jedimatt42/tipi/hardware/tipi-speech/kicad/3D/10-Pin Shrouded Header (IDC) Straight.stp

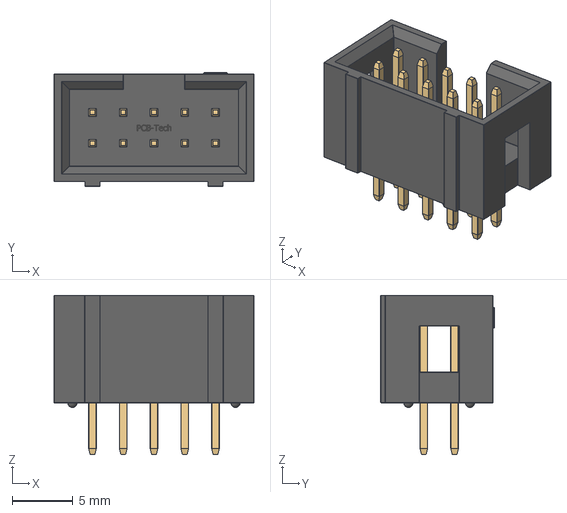
[picture p16: CAD file, 2020-05-09]
hardware/tipi-speech/kicad/3D/10-Pin Shrouded Header (IDC) Straight.stp
16.5 x 9.37 x 13.2 mm
Straight Contact x 10
10-Pin Shrouded Header Body
