jedimatt42/tipi/hardware/tipi-speech/kicad/3D/DS1021-2x5SF11.stp

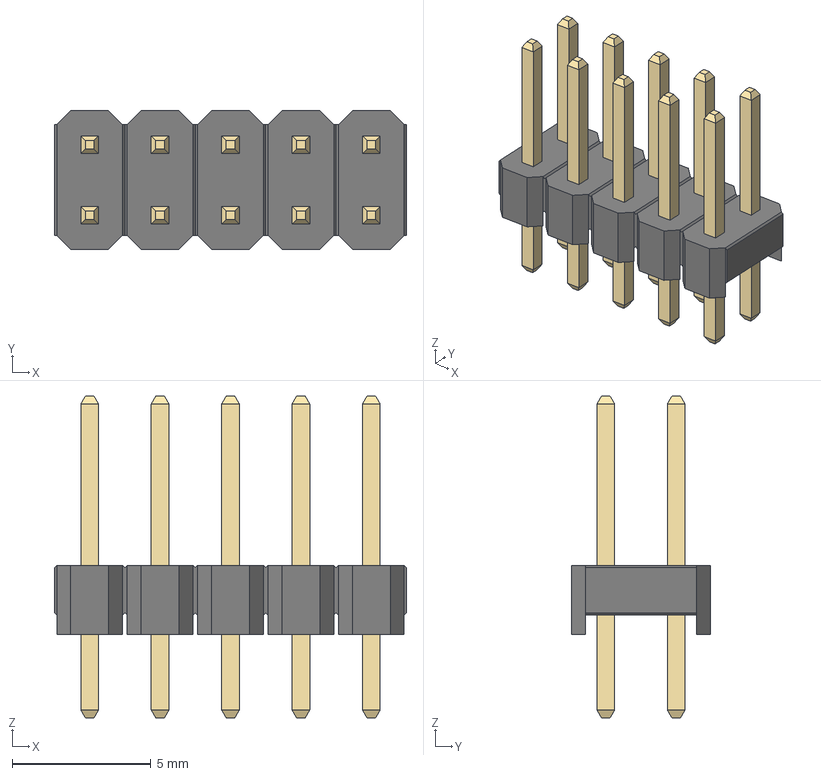
[picture p17: CAD file, 2020-05-09]
hardware/tipi-speech/kicad/3D/DS1021-2x5SF11.stp
12.7 x 5.00 x 11.6 mm
