jedimatt42/tipi/hardware/tipi-speech/kicad/3D/RC0805N.step

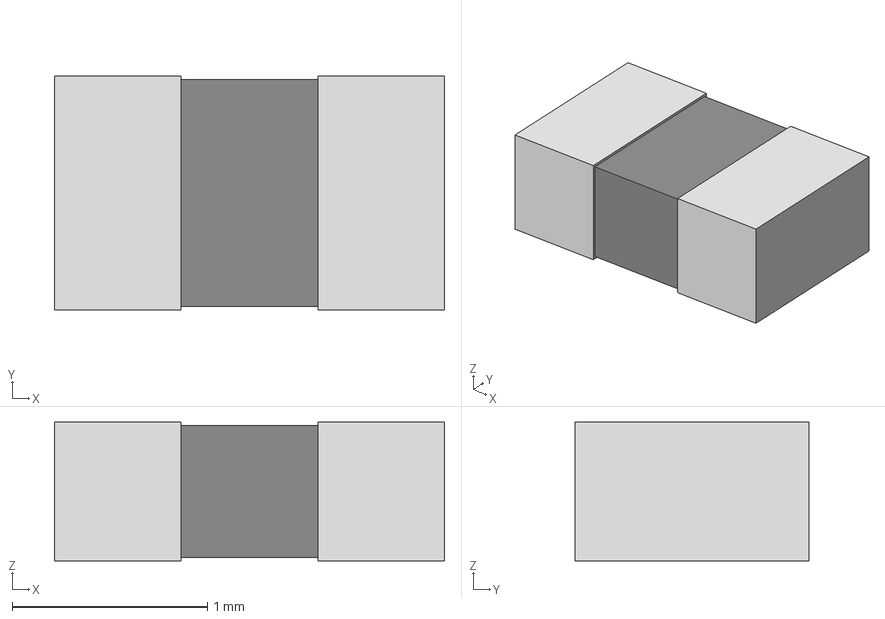
[picture p18: CAD file, 2020-05-09]
hardware/tipi-speech/kicad/3D/RC0805N.step
2.00 x 1.20 x 0.711 mm
