jedimatt42/tipi/hardware/tipi-speech/kicad/3D/67996-408HLF_AMP.step

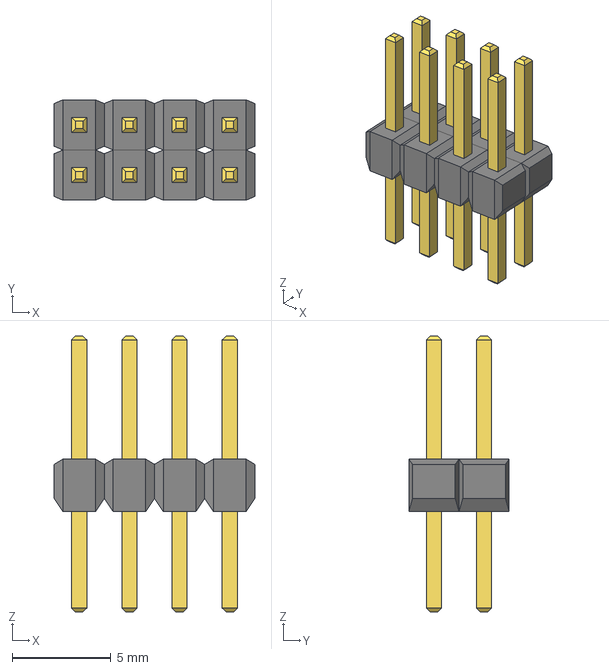
[picture p19: CAD file, 2020-05-09]
hardware/tipi-speech/kicad/3D/67996-408HLF_AMP.step
10.2 x 5.08 x 14.0 mm
