jedimatt42/tipi/hardware/tipi-speech/ise/tipi_top.v

`timescale 1ns / 1ps
//////////////////////////////////////////////////////////////////////////////////
// Company: 
// Engineer:  J-Data 99% reuse from TIPI
// 
// Create Date:    06/16/2020 
// Design Name: 
// Module Name:    tipi_top
// Project Name:   Tipi/32K
// Target Devices:  XC95144XL-10TQ100
// Tool versions:  17.1
// Description: 
//
// Dependencies: 
//
// Revision: 
// Revision V2 - File Created
// Additional Comments: 
//
//////////////////////////////////////////////////////////////////////////////////
`include "crubits.v"
`include "latch_8bit.v"
`include "shift_pload_sout.v"
`include "shift_sin_pout.v"
`include "tristate_8bit.v"
`include "mux2_8bit.v"
module tipi_top(
		output led0,
		
		input[0:3] crub,
		
		output db_dir,
		output db_en,
		output dsr_b0,
		output dsr_b1,
		output dsr_en,
		
		// Added to support 32K sram for TIPI-32K board
		output sram_a0,
		output sram_en,

		input r_clk,
		// 0 = Data or 1 = Control byte selection
		input r_cd,
		input r_dout,
		input r_le,
		// R|T 0 = RPi or 1 = TI originating data 
		input r_rt,
		output r_din,
		output r_reset,

		input ti_cruclk,
		input ti_dbin,
		input ti_memen,
		input ti_we,
		input ti_ph3,
		output ti_cruin,
		output ti_extint,
		
		input[0:15] ti_a,
		inout[0:7] tp_d
    );

// Unused
assign ti_extint = 1'bz; // try to avoid triggering this interrupt ( temporarily an input )

// Process CRU bits
wire ti_cruout = ti_a[15];
wire [0:3]cru_state;
wire cru_regout;
crubits cru((~crub[0:3] & 4'b0111), ti_cruclk, ti_memen, ti_ph3, ti_a[0:14], ti_cruout, cru_regout, cru_state);
wire cru_dev_en = cru_state[0];
assign ti_cruin = cru_regout;
assign r_reset = ~cru_state[1];
// For a 32k 27C256 chip, these control bank switching.
assign dsr_b0 = cru_state[2];
assign dsr_b1 = cru_state[3];
// For a 8k 27C64 chip, these need to stay constant
// assign dsr_b0 = 1'bz; // not connected on 27C64
// assign dsr_b1 = 1'b1; // Active LOW is PGM on 27C64

// Latches && Shift Registers for TI to RPi communication - TC & TD

// Register selection:
// r_rt and r_dc combine to select the rd rc td and tc registers. 
// we will assert that r_rt == 0 is RPi output register
//                     r_rt == 1 is TI output register
//                     r_dc == 0 is data register
//                     r_dc == 1 is control register
// The following aliases should help.
wire tipi_rc = ~r_rt && ~r_cd;
wire tipi_rd = ~r_rt && r_cd;
wire tipi_tc = r_rt && ~r_cd;
wire tipi_td = r_rt && r_cd; 

// address comparisons
wire rc_addr = ti_a == 16'h5ff9;
wire rd_addr = ti_a == 16'h5ffb;
wire tc_addr = ti_a == 16'h5ffd;
wire td_addr = ti_a == 16'h5fff;

// TD Latch
wire tipi_td_le = (cru_dev_en && ~ti_we && ~ti_memen && td_addr);
wire [0:7]rpi_td;
latch_8bit td(tipi_td_le, tp_d, rpi_td);

// TC Latch
wire tipi_tc_le = (cru_dev_en && ~ti_we && ~ti_memen && tc_addr);
wire [0:7]rpi_tc;
latch_8bit tc(tipi_tc_le, tp_d, rpi_tc);

// TD Shift output
wire td_out;
shift_pload_sout shift_td(r_clk, tipi_td, r_le, rpi_td, td_out);

// TC Shift output
wire tc_out;
shift_pload_sout shift_tc(r_clk, tipi_tc, r_le, rpi_tc, tc_out);


// Data from the RPi, to be read by the TI.

// RD
wire [0:7]tipi_db_rd;
wire rd_parity;
shift_sin_pout shift_rd(r_clk, tipi_rd, r_le, r_dout, tipi_db_rd, rd_parity);

// RC
wire [0:7]tipi_db_rc;
wire rc_parity;
shift_sin_pout shift_rc(r_clk, tipi_rc, r_le, r_dout, tipi_db_rc, rc_parity);

// Select if output is from the data or control register
reg r_din_mux;
always @(posedge r_clk) begin
  if (r_rt & r_cd) r_din_mux <= td_out;
  else if (r_rt & ~r_cd) r_din_mux <= tc_out;
  else if (~r_rt & r_cd) r_din_mux <= rd_parity;
  else r_din_mux <= rc_parity;
end
assign r_din = r_din_mux;

//-- Databus control
wire tipi_read = cru_dev_en && ~ti_memen && ti_dbin;
wire tipi_dsr_en = tipi_read && ti_a >= 16'h4000 && ti_a < 16'h5ff8;

// drive the dsr eprom oe and cs lines.
assign dsr_en = ~(tipi_dsr_en);


// drive the SRAM  enable and address MSB lines.   Added for TIPI-32K boards only.   Logic copied from 32K sidecar design except for disable. 
assign sram_en = ~(~ti_memen & ( (ti_a[0] &  ti_a[1]) | (~ti_a[1] &  ti_a[2])) & crub[0]);  // Enables (active low) 32K RAM on MEMEN low and address from 2000 to 3fff or A000 to FFFF, and on CRU MSB low (to disable internal RAM for CRU >=1800).  
assign sram_a0 = ti_a[0] & ti_a[2];  // Drives MSB Address line A14 on RAM, logic copied frm 32K sidecar design (A15 & A13).

// drive the 74hct245 data buffer oe and dir lines.  Modified to pass SRAM data for the TIPI-32K board only
assign db_en = ~((cru_dev_en && ti_a >= 16'h4000 && ti_a < 16'h6000) || ~sram_en);  //  Active low.  Added "( .. || ~sram_en)" to "or" tipi enable with SRAM eanble.  This will confict with external sram if not disabled.
assign db_dir = tipi_read | (~sram_en & ~ti_memen & ti_dbin);  // added "| (~sram_en & ~ti_memen & ti_dbin);"  to "or" sram read with tipi read for TIPI-32K board only.  


// register to databus output selection
wire [0:7]rreg_mux_out; 
mux2_8bit rreg_mux(rc_addr, tipi_db_rc, rd_addr, tipi_db_rd, tc_addr, rpi_tc, td_addr, rpi_td, rreg_mux_out);

wire [0:7]tp_d_buf;
wire dbus_ts_en = cru_state[0] && ~ti_memen && ti_dbin && ( ti_a >= 16'h5ff8 && ti_a < 16'h6000 );
tristate_8bit dbus_ts(dbus_ts_en, rreg_mux_out, tp_d_buf);

assign tp_d = tp_d_buf;


assign led0 = (cru_state[0] && db_en) || ~sram_en;  // Added SRAM activlty to TIPI LED activity 


endmodule
