jedimatt42/tipi/services/TipiSuper.py

#!/usr/bin/env python3
#

import os
import sys
import time
from subprocess import call


def configureWifi(wificonfig):
    # wait a couple seconds so file will be complete.
    time.sleep(2)
    # expect two config entries
    try:
        # read the username and password
        with open(wificonfig) as fh:
            ssid = fh.readline().rstrip()
            psk = fh.readline().rstrip()

        # remove handoff file
        os.remove(wificonfig)

        # adjust settings for network 0

        callargs = ["/usr/bin/raspi-config", "nonint", "do_wifi_ssid_passphrase", ssid, psk, "1"]
        print(f"Using raspi-config to connect to WiFi ssid ${ssid}")
        rescode = 1
        tries = 5
        while rescode != 0:
            rescode = call(callargs)
            if rescode != 0:
                print("failed to set WiFi config vi raspi-config, retrying...")
                tries = tries - 1
                if tries == 0:
                    raise Exception("failed to set WiFi config vi raspi-config")
            else:
                rescode = 0
                print("set WiFi config successfully")
    except Exception as e:
        print(e)


while True:
    time.sleep(1)

    # shutdown the PI safely
    if os.path.exists("/tmp/tipihalt"):
        os.remove("/tmp/tipihalt")
        callargs = ["/sbin/shutdown", "-h", "now"]
        if call(callargs) != 0:
            raise Exception("failed to run /sbin/shutdown")
        else:
            while True:
                time.sleep(20)

    # reboot the PI
    elif os.path.exists("/tmp/tipireboot"):
        os.remove("/tmp/tipireboot")
        callargs = ["/sbin/shutdown", "-r", "now"]
        if call(callargs) != 0:
            raise Exception("failed to run /sbin/shutdown")
        else:
            while True:
                time.sleep(20)

    # Configure WiFi from TI-side
    elif os.path.exists("/tmp/wificonfig"):
        configureWifi("/tmp/wificonfig")

    # Configure WiFi from bootstrap file on USB stick:
    elif os.path.exists("/media/usb1/tipiwifi.txt"):
        configureWifi("/media/usb1/tipiwifi.txt")

    # Upgrade TIPI services
    elif os.path.exists("/tmp/tipiupgrade"):
        os.remove("/tmp/tipiupgrade")
        callargs = ["/home/tipi/tipi/setup/upgrade.sh", "--upgrade"]
        if call(callargs) != 0:
            raise Exception("failed to run tipi upgrade")

    elif os.path.exists("/tmp/tz"):
        with open("/tmp/tz", "r") as tz_file:
            timezone = tz_file.readline().rstrip()
        callargs = ["/usr/bin/raspi-config", "nonint", "do_change_timezone", timezone]
        exitcode = call(callargs)
        os.remove("/tmp/tz")
        if exitcode:
            raise Exception("failed to set timezone {}".format(timezone))

    elif os.path.exists("/tmp/tipi_backup"):
        callargs = ["/home/tipi/tipi/setup/backup.sh"]
        exitcode = call(callargs)
        # do this last so webui can watch for it to go away
        os.remove("/tmp/tipi_backup")
        if exitcode:
            raise Exception("failed to create backup")

    elif os.path.exists("/tmp/tipi_restore"):
        callargs = ["/home/tipi/tipi/setup/restore.sh"]
        exitcode = call(callargs)
        if exitcode:
            raise Exception("failed to create backup")

    elif os.path.exists("/tmp/tipi_restart"):
        # restart some tipi services
        callargs = ["/home/tipi/tipi/setup/restart.sh"]
        exitcode = call(callargs)
        # do this last so webui can watch for it to go away
        os.remove("/tmp/tipi_restart")
        if exitcode:
            raise Exception("failed to restart services")
         
