jedimatt42/tipi/services/TiSocket.py

import os
import logging
import errno
import socket
import fcntl

# Represent socket access from Raw extensions.
# This is registered as 0x22 in RawExtensions.py
#
#  usage: send a message starting with 0x22 as the first byte.
#   second byte should be socket handle number to use
#   third byte is command for handle: 0x01 open, 0x02 close, 0x03 write, 0x04
#   read.
#
#   For 0x01 open / follow with string in the form of "hostname:port"
#     Tipi will return a message of 255 if connected or 0 if failed to connect.
#   For 0x02 close / no parameters
#     Tipi will return 255
#   For 0x03 write / follow with bytes to write to socket
#     Tipi will return after bytes are written with 255 or 0 if failed to
#     write.
#   For 0x04 read / follow with max size to read as int (two bytes, [msb,lsb])
#     Tipi will return message of available socket data no greater than max
#     size.
#
#   socket handle numbers are a single byte 0-255
#

logger = logging.getLogger(__name__)

GOOD = bytearray([255])
BAD = bytearray([0])
# It is ok, this is the same as good, but good isn't used in the context of accept.
ACCEPT_ERR = bytearray([255])


class TiSocket(object):
    def __init__(self, tipi_io):
        self.tipi_io = tipi_io
        self.handles = {}
        self.bindings = {}
        self.commands = {
            0x01: self.handleOpen,
            0x02: self.handleClose,
            0x03: self.handleWrite,
            0x04: self.handleRead,
            0x05: self.handleBind,
            0x06: self.handleUnbind,
            0x07: self.handleAccept,
        }

    def handle(self, bytes):
        self.tipi_io.send(self.processRequest(bytes))
        return True

    def processRequest(self, bytes):
        try:
            command = bytes[2]
            commandHandler = self.commands.get(command, self.defaultHandler)
            return commandHandler(bytes)
        except IOError:
            return BAD

    def defaultHandler(self, bytes):
        logger.error("unknown command: %d", bytes[2])
        return BAD

    # bytes: 0x22, handleId, open-cmd, <hostname:port>
    def handleOpen(self, bytes):
        sock = None
        try:
            handleId = bytes[1]
            params = str(bytes[3:], 'ascii').split(":")
            hostname = params[0]
            port = int(params[1])
            logger.info("open socket(%d) %s:%d", handleId, hostname, port)

            existing = self.handles.get(handleId, None)
            # close the socket if we already had one for this handle.
            if existing is not None:
                del self.handles[handleId]
                self.safeClose(existing)
                existing = None
                logger.debug("closed leftover socket: %d", handleId)
            # need to get the target host and port
            server = (hostname, port)
            sock = socket.socket(socket.AF_INET, socket.SOCK_STREAM)
            self.handles[handleId] = sock

            sock.connect(server)
            fcntl.fcntl(sock, fcntl.F_SETFL, os.O_NONBLOCK)
            logger.info("connected")
            return GOOD
        except Exception:
            logger.info("failed to connect socket: %d", handleId)
            self.safeClose(sock)
            return BAD

    # bytes: 0x22, handleId, close-cmd
    def handleClose(self, bytes):
        handleId = bytes[1]
        existing = self.handles.get(handleId, None)
        if existing is not None:
            del self.handles[handleId]
            self.safeClose(existing)
            logger.info("closed socket: %d", handleId)
        return GOOD

    # bytes: 0x22, handleId, write-cmd, <bytes to write>
    def handleWrite(self, bytes):
        handleId = bytes[1]
        if not handleId in self.handles.keys():
            logger.info("No socket open for handleId %s", handleId)
            return BAD
        try:
            existing = self.handles[handleId]
            existing.sendall(bytes[3:])
            logger.debug("wrote %d bytes to socket: %d", len(bytes[3:]), handleId)
            return GOOD
        except Exception:
            del self.handles[handleId]
            self.safeClose(existing)
            logger.info("failed to write to socket: %d", handleId)
            return BAD

    # bytes: 0x22, handleId, read-cmd, MSB, LSB
    def handleRead(self, bytes):
        try:
            handleId = bytes[1]
            logger.debug("read socket: %d", handleId)
            existing = self.handles.get(handleId, None)
            if existing is None:
                logger.info("socket not open: %d", handleId)
                return bytearray(0)
            limit = (bytes[3] << 8) + bytes[4]
            data = bytearray(existing.recv(limit))
            logger.info("read %d bytes from %d", len(data), handleId)
            return data
        except socket.error as e:
            err = e.args[0]
            if err == errno.EAGAIN or err == errno.EWOULDBLOCK:
                logger.debug("no data ready: %d", handleId)
                return bytearray(0)
            else:
                logger.error(e, exc_info=True)
        except Exception as e:
            logger.error(e, exc_info=True)
        return BAD

    def handleBind(self, bytes):
        serverId = bytes[1]
        params = str(bytes[3:], 'ascii').split(":")
        interface = params[0]
        port = int(params[1])
        logger.info("bind socket(%d) %s:%d", serverId, interface, port)

        existing = self.bindings.get(serverId, None)
        # close the socket if we already had one for this handle.
        if existing is not None:
            del self.bindings[serverId]
            self.safeClose(existing)
            existing = None
            logger.debug("closed leftover binding: %d", serverId)
        # need to get the target host and port
        if interface == "*":
            interface = "0.0.0.0"
        server = (interface, port)
        sock = socket.socket(socket.AF_INET, socket.SOCK_STREAM)
        sock.setblocking(0)
        try:
            sock.bind(server)
            self.bindings[serverId] = sock
            sock.listen(5)
            logger.info("bind success")
            return GOOD
        except Exception:
            logger.info("failed to bind socket: %d", serverId, exc_info=True)
            self.safeClose(sock)
            return BAD

    def handleUnbind(self, bytes):
        serverId = bytes[1]
        if serverId in self.bindings.keys():
            existing = self.bindings.get(serverId, None)
            del self.bindings[serverId]
            self.safeClose(existing)
            logger.info("unbound socket: %d", serverId)
        return GOOD

    def handleAccept(self, bytes):
        logger.info("handleAccept")
        serverId = bytes[1]
        server_socket = self.bindings.get(serverId, None)
        if server_socket is not None:
            handleId = self.allocateHandleId()
            logger.info("new connection handle: %d", handleId)
            if handleId == 0:
                logger.error("out of handles")
                return ACCEPT_ERR
            logger.info("accepting...")
            conn = None
            try:
                conn, address = server_socket.accept()
            except Exception as e:
                logger.info("no connection available")
                return BAD
            logger.info("accept conn: %s", conn)
            if conn:
                fcntl.fcntl(conn, fcntl.F_SETFL, os.O_NONBLOCK)
                self.handles[handleId] = conn
                logger.info("connection socket given handleId %d", handleId)
                return bytearray([handleId])
            else:
                logger.info("no connection available")
                return BAD
        else:
            logger.error("no socket bound with id: %d", serverId)
            return ACCEPT_ERR

    def safeClose(self, sock):
        try:
            if sock:
                logger.info("closing socket")
                sock.shutdown(socket.SHUT_RDWR)
                sock.close()
        except Exception:
            pass

    def allocateHandleId(self):
        handleId = 1
        while handleId < 256:
            if handleId not in self.handles.keys():
                return handleId
            handleId += 1
        logger.info("out of handles")
        return 0
