jedimatt42/tipi/clients/tipiman/oem_high_chars.asm

	DEF PAT127

****************************************
* High Character Patterns                    
****************************************
PAT127 DATA >0000,>1028,>4444,>7C00    ;
PAT128 DATA >3844,>4040,>4438,>0818    ;
PAT129 DATA >2800,>4444,>4C34,>0000    ;
PAT130 DATA >0810,>3844,>7C40,>3800    ;
PAT131 DATA >1028,>0038,>444C,>3400    ;
PAT132 DATA >0028,>0038,>444C,>3400    ;
PAT133 DATA >2010,>0038,>444C,>3400    ;
PAT134 DATA >1028,>1038,>444C,>3400    ;
PAT135 DATA >0038,>4440,>4438,>0818    ;
PAT136 DATA >1028,>0038,>447C,>4038    ;
PAT137 DATA >2800,>3844,>7C40,>3800    ;
PAT138 DATA >2010,>0038,>447C,>4038    ;
PAT139 DATA >0028,>0030,>1038,>0000    ;
PAT140 DATA >1028,>0030,>1038,>0000    ;
PAT141 DATA >2010,>0030,>1038,>0000    ;
PAT142 DATA >2800,>3844,>7C44,>4400    ;
PAT143 DATA >1028,>1038,>447C,>4444    ;
PAT144 DATA >0810,>007C,>4078,>407C    ;
PAT145 DATA >0000,>6814,>3850,>2C00    ;
PAT146 DATA >3C50,>507C,>5050,>5C00    ;
PAT147 DATA >1028,>0038,>4444,>3800    ;
PAT148 DATA >0028,>0038,>4444,>3800    ;
PAT149 DATA >2010,>0038,>4444,>3800    ;
PAT150 DATA >1028,>0044,>444C,>3400    ;
PAT151 DATA >2010,>0044,>444C,>3400    ;
PAT152 DATA >0028,>0044,>4438,>0870    ;
PAT153 DATA >2838,>4444,>4444,>3800    ;
PAT154 DATA >2800,>4444,>4444,>3800    ;
PAT155 DATA >0010,>3C50,>503C,>1000    ;
PAT156 DATA >1820,>2070,>2020,>7C00    ;
PAT157 DATA >4444,>287C,>107C,>1000    ;
PAT158 DATA >0068,>5C58,>7C54,>5C00    ;
PAT159 DATA >0408,>1C08,>0808,>1000    ;
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
PAT249 DATA >0020,>7020,>0000,>0000    ;
PAT250 DATA >0030,>3000,>0000,>0000    ;
PAT251 DATA >0404,>0408,>6828,>1000    ;
PAT252 DATA >0060,>5050,>0000,>0000    ;
PAT253 DATA >6010,>2070,>0000,>0000    ;
PAT254 DATA >0000,>F8F8,>F8F8,>0000    ;
PAT255 DATA >0000,>0000,>0000,>0000    ;
