jedimatt42/tipi/hardware/tipi-speech/ise/shift_pload_sout.v

`ifndef _shift_pload_sout_vh_
`define _shift_pload_sout_vh_

module shift_pload_sout (
    // Clock for shifting
    input clk,
	 // Select
	 input select,
	 // load tmp with data to shift out.
    input aload,
	 // Data to load from
    input [7:0]data,
	 // output bit from the left.
    output sout
);

reg [8:0]tmp;

always @(posedge clk) begin
  if (aload && select) tmp = { data, ^data };
  else if (select) tmp = { tmp[7:0], 1'b0 };
end

assign sout = tmp[8];

endmodule

`endif
