jedimatt42/tipi/clients/tipiman/oem_low_chars.asm

	DEF PAT0

****************************************
* low order Character Patterns                    
****************************************
PAT0   DATA >0000,>0000,>0000,>0000    ;
PAT1   DATA >0078,>84AC,>84B4,>8478    ;
PAT2   DATA >0078,>FCD4,>FCCC,>FC78    ;
PAT3   DATA >0000,>6C7C,>7C38,>1000    ;
PAT4   DATA >0000,>1038,>7C38,>1000    ;
PAT5   DATA >0000,>3030,>FCEC,>2020    ;
PAT6   DATA >0000,>1038,>7C7C,>6C10    ;
PAT7   DATA >0000,>0020,>7020,>0000    ;
PAT8   DATA >FCFC,>FCDC,>8CDC,>FCFC    ;
PAT9   DATA >0030,>4884,>8448,>3000    ;
PAT10  DATA >FCCC,>B478,>78B4,>CCFC    ;
PAT11  DATA >001C,>0C74,>9090,>6000    ;
PAT12  DATA >0070,>8888,>7020,>7020    ;
PAT13  DATA >0018,>1410,>1070,>6000    ;
PAT14  DATA >0018,>1414,>1474,>6C18    ;
PAT15  DATA >0010,>5428,>2854,>1000    ;
PAT16  DATA >0000,>0060,>7860,>0000    ;
PAT17  DATA >0000,>0018,>7818,>0000    ;
PAT18  DATA >0000,>2070,>2020,>7020    ;
PAT19  DATA >0050,>5050,>5000,>5000    ;
PAT20  DATA >0070,>D0D0,>5050,>5000    ;
PAT21  DATA >0070,>8070,>8870,>0870    ;
PAT22  DATA >0000,>00FC,>FCFC,>0000    ;
PAT23  DATA >0020,>7020,>2070,>2070    ;
PAT24  DATA >0020,>70A8,>2020,>2000    ;
PAT25  DATA >0020,>2020,>A870,>2000    ;
PAT26  DATA >0000,>2010,>F810,>2000    ;
PAT27  DATA >0000,>2040,>F840,>2000    ;
PAT28  DATA >8080,>8080,>80FC,>0000    ;
PAT29  DATA >0000,>0048,>FC48,>0000    ;
PAT30  DATA >0000,>2020,>7070,>0000    ;
PAT31  DATA >0000,>7070,>2020,>0000    ;
