jedimatt42/tipi/examples/mouse/patterns.asm

	def gfx_point0
	def gfx_point1

****************************************
* Sprite Patterns                       
****************************************
gfx_point0
	DATA >FF81,>8284,>8291,>A8C4    ; Color 1
	DATA >0201,>0000,>0000,>0000    ; 
	DATA >0000,>0000,>0000,>8040    ; 
	DATA >8000,>0000,>0000,>0000    ; 
gfx_point1
	DATA >007E,>7C78,>7C6E,>4703    ; Color 15
	DATA >0100,>0000,>0000,>0000    ; 
	DATA >0000,>0000,>0000,>0080    ; 
	DATA >0000,>0000,>0000,>0000    ; 
